SamuelNoesslboeck/DrRoll/documentation/captures/3_cad_progress_24_12_01.png

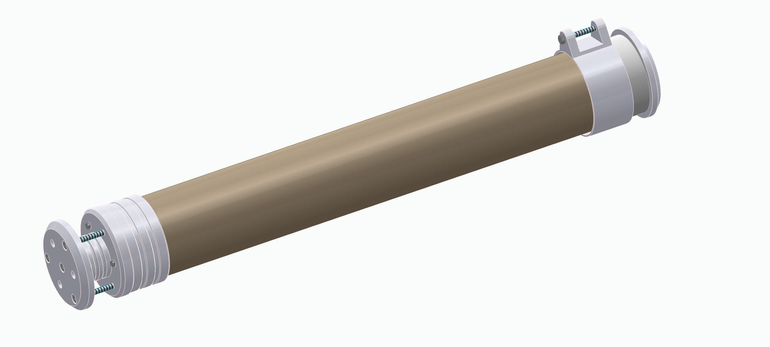
documentation/captures/3_cad_progress_24_12_01.png
